dcbeelinekz2/ToyRep/3D print/ToyREP-Z_Joint.stl

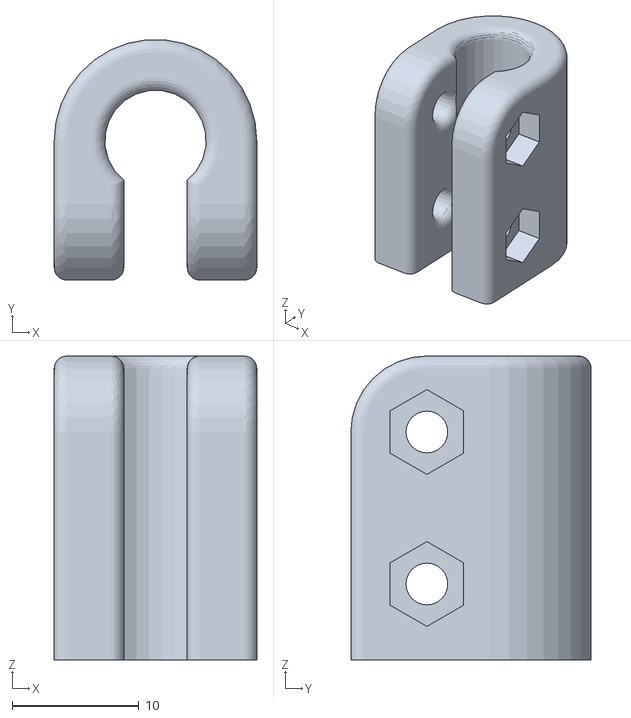
[picture p73: CAD file, 2018-01-18]
3D print/ToyREP-Z_Joint.stl
16.0 x 19.0 x 24.0
