dcbeelinekz2/ToyRep/3D print/ToyREP-Z1.stl

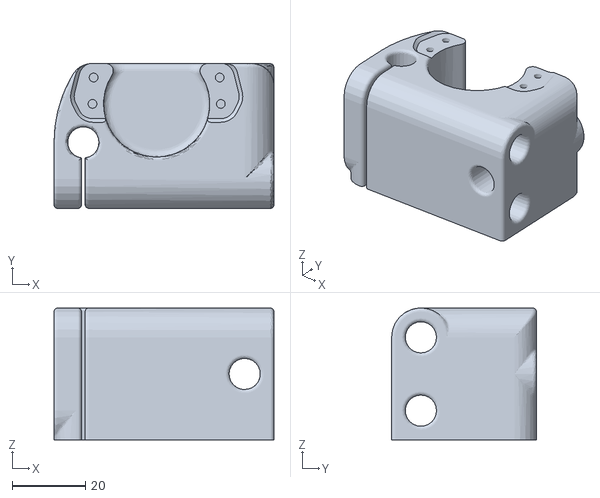
[picture p74: CAD file, 2018-01-18]
3D print/ToyREP-Z1.stl
60.0 x 39.5 x 36.0
