dcbeelinekz2/ToyRep/3D print/ToyREP-Frog.stl

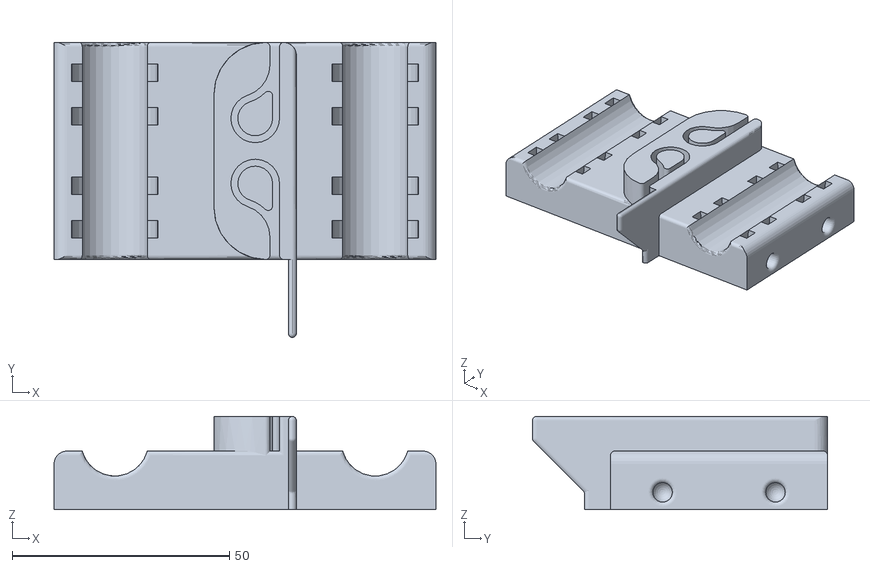
[picture p75: CAD file, 2018-01-18]
3D print/ToyREP-Frog.stl
88.0 x 68.0 x 21.5
