dcbeelinekz2/ToyRep/3D print/ToyREP-PCB-1.stl

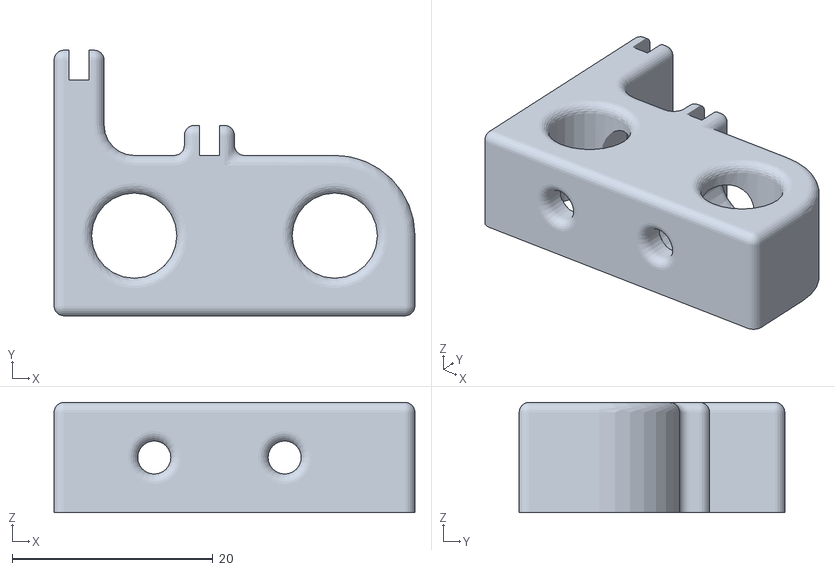
[picture p76: CAD file, 2018-01-18]
3D print/ToyREP-PCB-1.stl
36.0 x 26.5 x 11.0
