dcbeelinekz2/ToyRep/3D print/ToyREP-Idler.stl

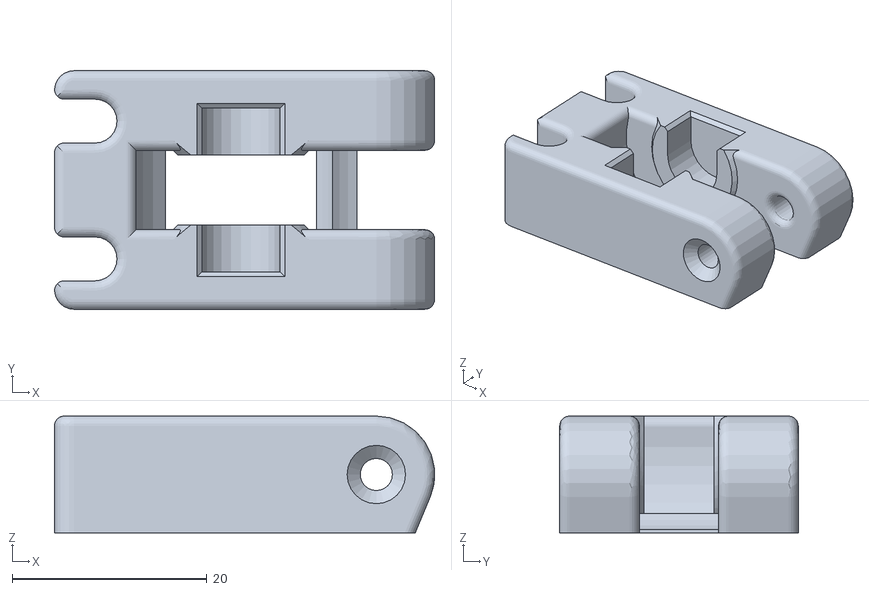
[picture p77: CAD file, 2018-01-18]
3D print/ToyREP-Idler.stl
39.0 x 24.5 x 12.0
