dcbeelinekz2/ToyRep/3D print/ToyREP-Pinion.stl

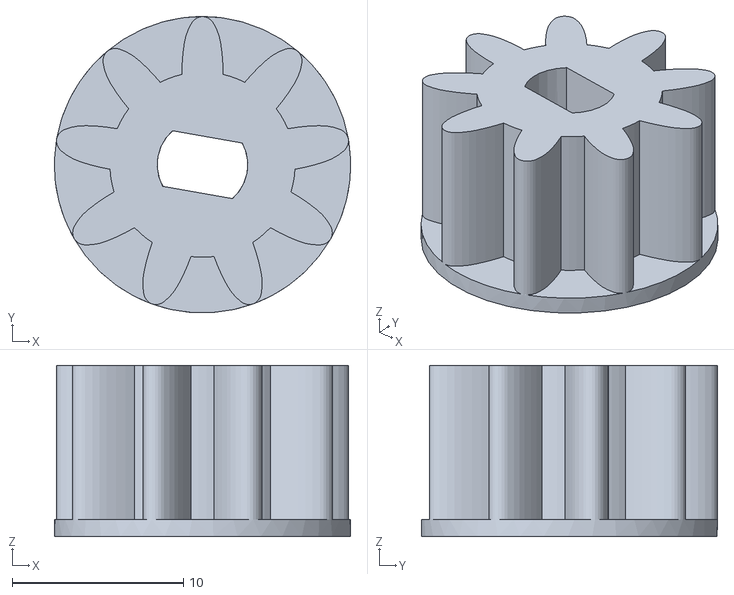
[picture p78: CAD file, 2018-01-18]
3D print/ToyREP-Pinion.stl
17.3 x 17.3 x 10.00
