dcbeelinekz2/ToyRep/3D print/ToyREP-X1.stl

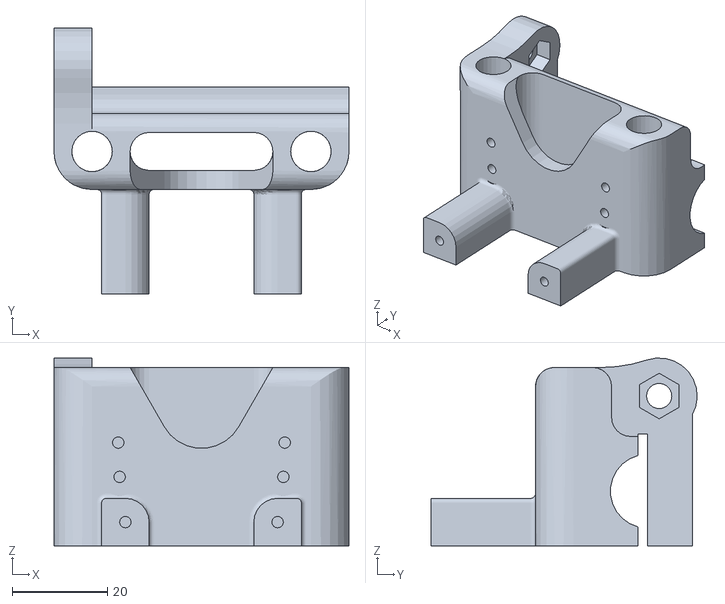
[picture p79: CAD file, 2018-01-18]
3D print/ToyREP-X1.stl
62.0 x 56.0 x 39.5
